pixelcircuits/GBConsole_Documentation/guide/img/gbconsole_scn3.jpg

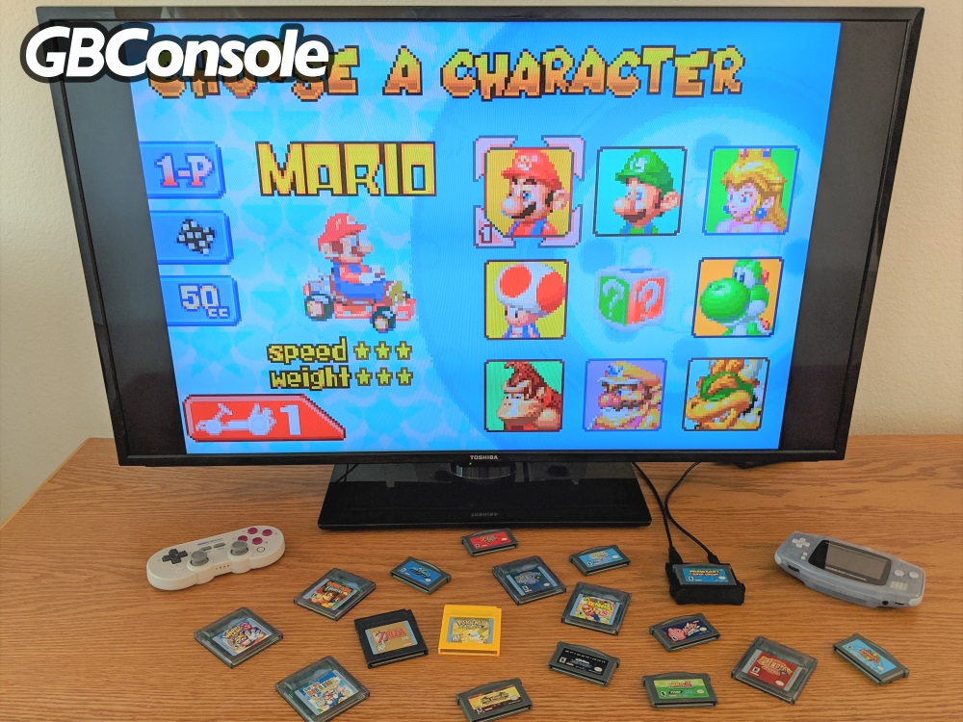
guide/img/gbconsole_scn3.jpg
